croftj/nixiestat/code/core/PID.cpp

/**********************************************************************************************
 * Arduino PID Library - Version 1.0.1
 * by Brett Beauregard <br3ttb@gmail.com> brettbeauregard.com
 *
 * This Library is licensed under a GPLv3 License
 **********************************************************************************************/

#if ARDUINO >= 100
  #include "Arduino.h"
#else
  #include "WProgram.h"
#endif

#include <PID.h>

//#define DBG

/*Constructor (...)*********************************************************
 *    The parameters specified here are those for for which we can't set up 
 *    reliable defaults, so we need to have the user set them.
 ***************************************************************************/
PID::PID(double Kp, double Ki, double Kd, int ControllerDirection) :
      m_debug(false)
{
   inAuto = false;
   SampleTime = 100;
   PID::SetOutputLimits(0, 255);          //default output limit corresponds to 
   PID::SetControllerDirection(ControllerDirection);
   PID::SetTunings(Kp, Ki, Kd);
   ITerm = 0.0;
}
 
 
/* Compute() **********************************************************************
 *     This, as they say, is where the magic happens.  this function should be called
 *   every time "void loop()" executes.  the function will decide for itself whether a new
 *   pid Output needs to be computed.  returns true when the output is computed,
 *   false when nothing has been done.
 **********************************************************************************/ 
double PID::Compute(double input)
{
//   if (!inAuto) return false;
   /*Compute all the working error variables*/
   m_input = input;
   double error = m_target - m_input;

   double SampleTimeInSec = ((double)SampleTime)/1000;  
   ITerm += (ki * error);
   if (ITerm > ki * (600 / SampleTimeInSec)) 
      ITerm = ki * ((600 - 50) / SampleTimeInSec);
   if (ITerm < ki * -(600 / SampleTimeInSec)) 
      ITerm = ki * -((600 - 50) / SampleTimeInSec);
   double dInput = (m_input - lastInput);

   if ( m_debug ) 
   {
      Serial << "SampleTime = " << SampleTime << endl;
      Serial << "error = " << error << endl;
      Serial << "Kp = " << dispKp << " (" << kp << ")" << endl;
      Serial << "Ki = " << dispKi << " (" << ki << ")" << endl;
      Serial << "Kd = " << dispKd << " (" << kd << ")" << endl;
   }

   /*Compute PID Output*/
   double PTerm = kp * error;
   double DTerm = kd * dInput;
   m_output = PTerm + ITerm - DTerm;
   if ( m_debug ) 
   {
      Serial << "PTerm = " << PTerm;
      Serial << ", ITerm = " << ITerm;   
      Serial << ", DTerm = " << DTerm;   
      Serial << ", raw output = " << m_output;   
   }
   if (m_output > outMax) 
      m_output = outMax;
//   else if (m_output < outMin) 
//      m_output = outMin;
   if ( m_debug ) 
   {
      Serial << ", limited output = " << m_output;   
      Serial << endl;
   }
   /*Remember some variables for next time*/
   lastInput = m_input;
   return(m_output);
}

void PID::SetTarget(double target)
{
   m_target = target;

   if ( m_debug ) 
   {
      Serial << "m_target = " << m_target << endl;
   }
}

/* SetTunings(...)*************************************************************
 * This function allows the controller's dynamic performance to be adjusted. 
 * it's called automatically from the constructor, but tunings can also
 * be adjusted on the fly during normal operation
 ******************************************************************************/ 
void PID::SetTunings(double Kp, double Ki, double Kd)
{
   if (Kp < 0 || Ki < 0 || Kd < 0) 
      return;
 
   dispKp = Kp; 
   dispKi = Ki; 
   dispKd = Kd;
   
   double SampleTimeInSec = ((double)SampleTime)/1000;  
   kp = Kp;
   ki = Ki * SampleTimeInSec;
   kd = Kd / SampleTimeInSec;

   if ( m_debug ) 
   {
      Serial << "controllerDirection = " << controllerDirection << endl;
      Serial << "SampleTime = " << SampleTime << endl;
      Serial << "Kp = " << dispKp << " (" << kp << ")" << endl;
      Serial << "Ki = " << dispKi << " (" << ki << ")" << endl;
      Serial << "Kd = " << dispKd << " (" << kd << ")" << endl;
   }

   if(controllerDirection ==REVERSE)
   {
      kp = (0 - kp);
      ki = (0 - ki);
      kd = (0 - kd);
   }
}
  
/* SetSampleTime(...) *********************************************************
 * sets the period, in Milliseconds, at which the calculation is performed 
 ******************************************************************************/
void PID::SetSampleTime(int NewSampleTime)
{
   if (NewSampleTime > 0)
   {
      double ratio  = (double)NewSampleTime
                      / (double)SampleTime;
      ki *= ratio;
      kd /= ratio;

      SampleTime = (unsigned long)NewSampleTime;

      if ( m_debug ) 
      {
         Serial << "SampleTime = " << SampleTime << endl;
         Serial << "Kp = " << dispKp << " (" << kp << ")" << endl;
         Serial << "Ki = " << dispKi << " (" << ki << ")" << endl;
         Serial << "Kd = " << dispKd << " (" << kd << ")" << endl;
      }
   }
}
 
/* SetOutputLimits(...)****************************************************
 *     This function will be used far more often than SetInputLimits.  while
 *  the input to the controller will generally be in the 0-1023 range (which is
 *  the default already,)  the output will be a little different.  maybe they'll
 *  be doing a time window and will need 0-8000 or something.  or maybe they'll
 *  want to clamp it from 0-125.  who knows.  at any rate, that can all be done
 *  here.
 **************************************************************************/
void PID::SetOutputLimits(double Min, double Max)
{
   if(Min >= Max) return;
   outMin = Min;
   outMax = Max;
 
   if(inAuto)
   {
      if (m_output > outMax) 
         m_output = outMax;
      else if(m_output < outMin) 
         m_output = outMin;
    
      if (ITerm > outMax) 
         ITerm = outMax;
      else if (ITerm < outMin) 
         ITerm = outMin;
   }
}

/* SetMode(...)****************************************************************
 * Allows the controller Mode to be set to manual (0) or Automatic (non-zero)
 * when the transition from manual to auto occurs, the controller is
 * automatically initialized
 ******************************************************************************/ 
void PID::SetMode(int Mode)
{
    bool newAuto = (Mode == AUTOMATIC);
    if(newAuto == !inAuto)
    {  /*we just went from manual to auto*/
        PID::Initialize();
    }
    inAuto = newAuto;
}
 
/* Initialize()****************************************************************
 * does all the things that need to happen to ensure a bumpless transfer
 *  from manual to automatic mode.
 ******************************************************************************/ 
void PID::Initialize()
{
   ITerm = m_output;
   lastInput = m_input;
   if (ITerm > outMax) 
      ITerm = outMax;
   else if (ITerm < outMin)
      ITerm = outMin;
}

/* SetControllerDirection(...)*************************************************
 * The PID will either be connected to a DIRECT acting process (+Output leads 
 * to +Input) or a REVERSE acting process(+Output leads to -Input.)  we need to
 * know which one, because otherwise we may increase the output when we should
 * be decreasing.  This is called from the constructor.
 ******************************************************************************/
void PID::SetControllerDirection(int Direction)
{
   if(inAuto && Direction !=controllerDirection)
   {
      kp = (0 - kp);
      ki = (0 - ki);
      kd = (0 - kd);
   }   
   controllerDirection = Direction;
}

/* Status Funcions*************************************************************
 * Just because you set the Kp=-1 doesn't mean it actually happened.  these
 * functions query the internal state of the PID.  they're here for display 
 * purposes.  this are the functions the PID Front-end uses for example
 ******************************************************************************/
double PID::GetKp()
{ 
   return  dispKp; 
}

double PID::GetKi()
{ 
   return  dispKi;
}

double PID::GetKd()
{ 
   return  dispKd;
}

int PID::GetMode()
{
   return  inAuto ? AUTOMATIC : MANUAL;
}

int PID::GetDirection()
{
   return controllerDirection;
}

double PID::GetOutput()
{
   return m_output;
}
