croftj/nixiestat/code/UiStateMachine.cpp

# include "UiStateMachine.h"

# include "datetime.h"
# include "ui.h"

static uint8_t                dbg = true;
static uint8_t                dbg1 = true;

static UI_Idle                state_Idle("Idle");
static UI_Awake               state_Awake("Awake");
static UI_ShowTemp            state_ShowTemp("ShowTemp");
static UI_MinuteAdvance       state_MinuteAdvance("MinuteAdvance");
static UI_HourAdvance         state_HourAdvance("HourAdvance");
static UI_TemperatureAdvance  state_TemperatureAdvance("TemperatureAdvance");
static UI_DayAdvance          state_DayAdvance("DayAdvance");
static UI_MonthAdvance        state_MonthAdvance("MonthAdvance");
static UI_YearAdvance         state_YearAdvance("YearAdvance");
static UI_HeatCool            state_HeatCool("HeatCool");
static UI_ModeAdvance         state_ModeAdvance("ModeAdvance");

UIState*  UIState::m_initialState;

/**********************************************************************/
/*   Idle  State,  this state disables the display and waits for any  */
/*   activity on the touch pannel                                     */
/**********************************************************************/
UI_Idle::UI_Idle(const char *my_name) : UIState(my_name), m_index(1)
{
   m_initialState = this;
   m_index = 0;
}

void UI_Idle::initEvent()
{
   if (dbg) Serial << __PRETTY_FUNCTION__ << " here" << endl;
//   ui.setState( &state_Awake );
}

void UI_Idle::upEvent()
{
   if (dbg) Serial << __PRETTY_FUNCTION__ << " here" << endl;
//   ui.setState( &state_Awake );
}

void UI_Idle::downEvent()
{
   if (dbg) Serial << __PRETTY_FUNCTION__ << " here" << endl;
//   ui.setState( &state_Awake );
}

void UI_Idle::modeEvent()
{
   if (dbg) Serial << __PRETTY_FUNCTION__ << " here" << endl;
//   ui.setState( &state_Awake );
}

void UI_Idle::stepEvent()
{
   if (dbg) Serial << __PRETTY_FUNCTION__ << " here" << endl;
//   ui.setState( &state_Awake );
}

void UI_Idle::setEvent()
{
   if (dbg) Serial << __PRETTY_FUNCTION__ << " here" << endl;
   ui.saveSettings();
//   ui.setState( &state_Awake );
}

void UI_Idle::clearEvent()
{
   if (dbg) Serial << __PRETTY_FUNCTION__ << " here" << endl;
   ui.flashNone();
//   ui.setState( &state_Awake );
}

void UI_Idle::timeShortEvent()
{
   m_index++;
   if ( m_index > 3 ) 
   {
      m_index = 0;
   }
   ui.ShowTimeTemp( m_index );
}

void UI_Idle::wakenEvent()
{
   if (dbg) Serial << __PRETTY_FUNCTION__ << " here" << endl;
//   ui.setState( &state_Awake );
}


void UI_Idle::onEntry()
{
   if (dbg) Serial << __PRETTY_FUNCTION__ << " here" << endl;
   ui.clearLamps();
   ui.flashNone();
//   ui.displayOff();
}
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
